VeniVidiReliqui/split_print/pics/IMG_8840.jpeg

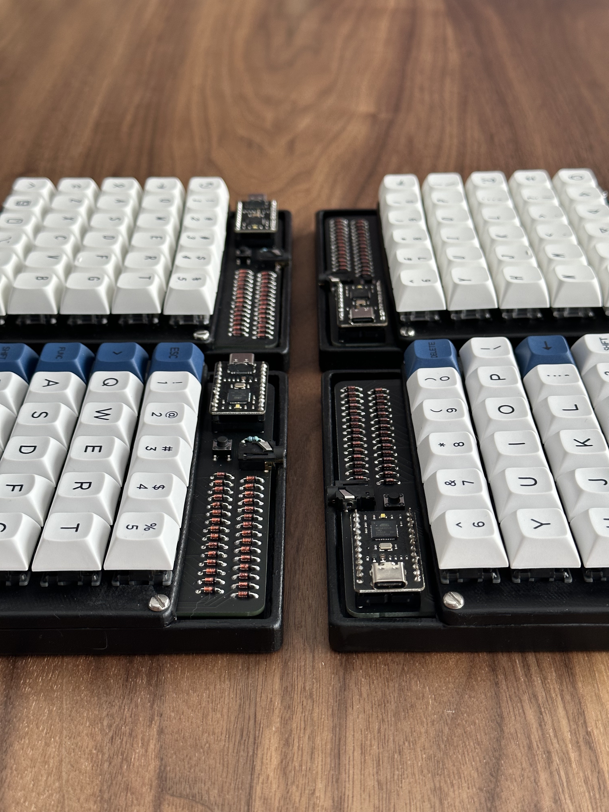
pics/IMG_8840.jpeg
