VeniVidiReliqui/split_print/pics/IMG_8841.jpeg

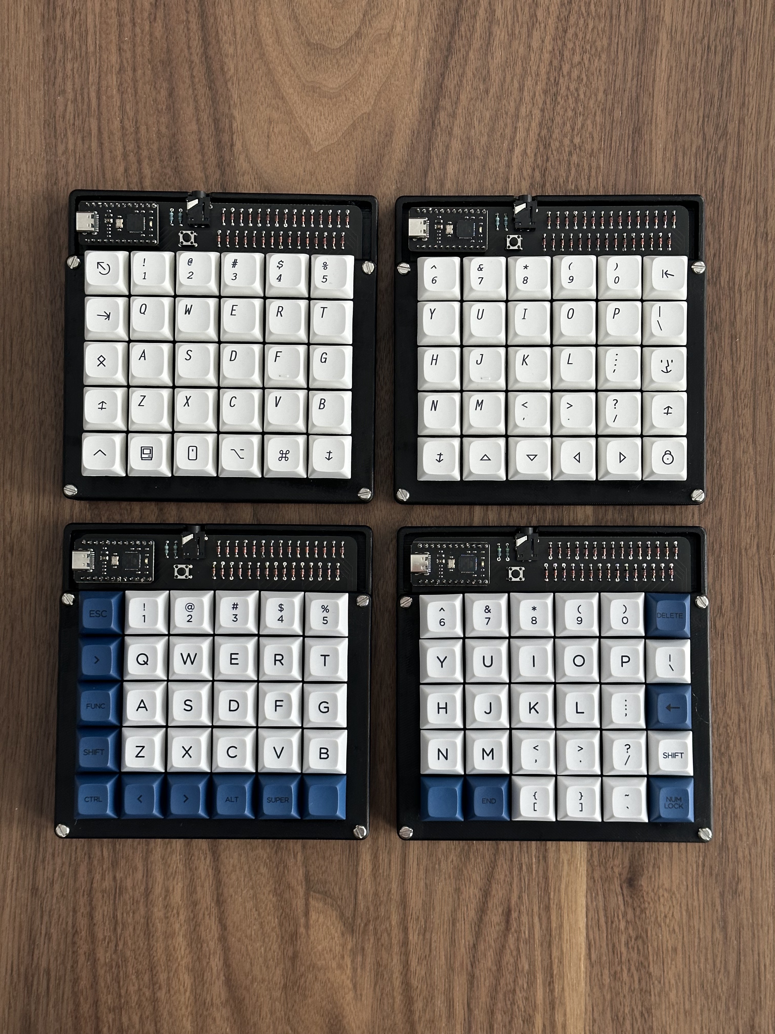
pics/IMG_8841.jpeg
