VeniVidiReliqui/split_print/pics/IMG_8843.jpeg

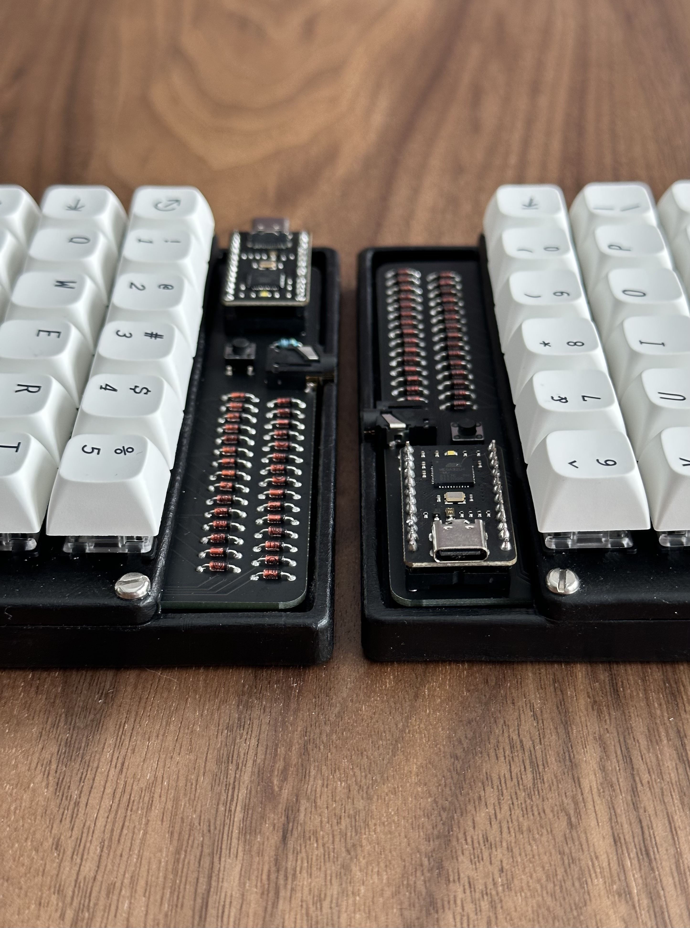
pics/IMG_8843.jpeg
