VeniVidiReliqui/split_print/pics/IMG_8845.jpeg

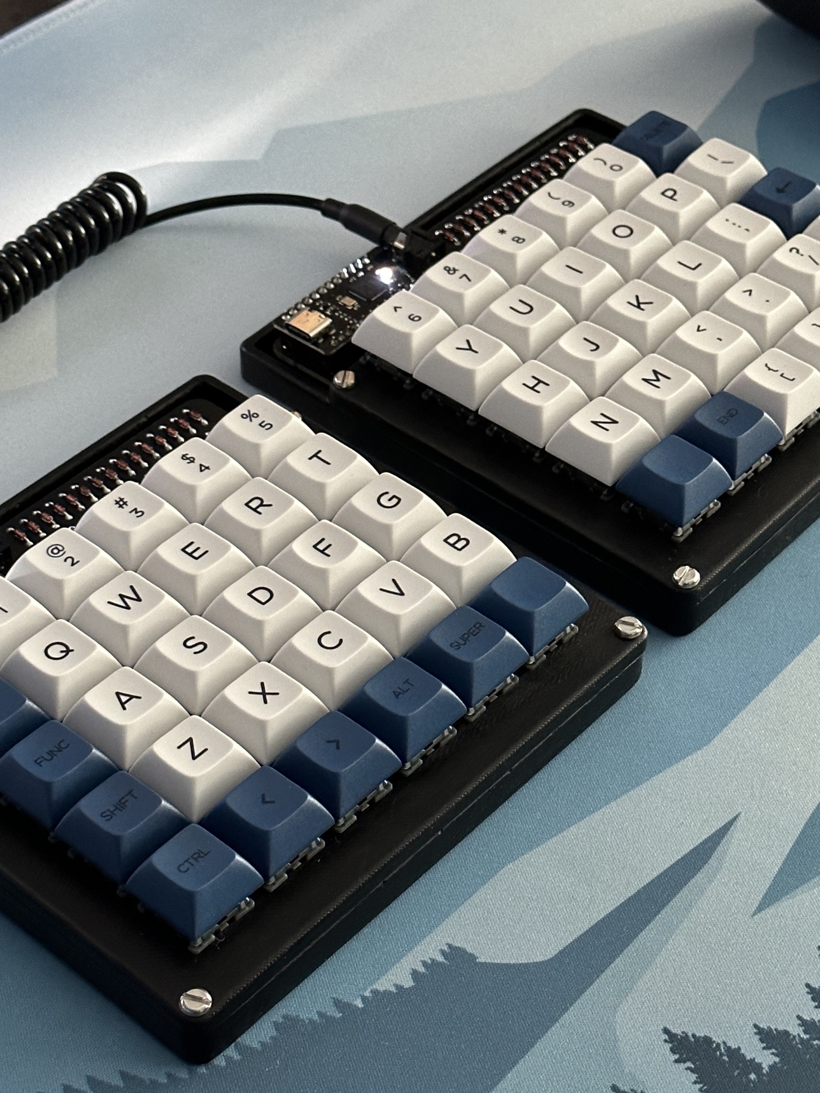
pics/IMG_8845.jpeg
